valex2/kairos/KairosV1/Data/test_temp_light.csv

Timestamp | Temperature | Gas | Humidity | Pressure | Altitude | Visible Light | IR Light
0.3 | 25.8 | 147592 | 47.9 | 1009.0 | 35.1 | 145.0 | 142.0
0.6 | 25.8 | 71210 | 47.6 | 1009.0 | 35.2 | 141.0 | 143.0
0.9 | 25.9 | 86340 | 47.3 | 1009.0 | 35.2 | 141.0 | 143.0
1.2 | 25.9 | 96240 | 46.9 | 1009.0 | 35.2 | 83.0 | 77.0
1.5 | 26.0 | 102728 | 46.5 | 1009.0 | 35.2 | 113.0 | 112.0
1.8 | 26.0 | 107180 | 46.1 | 1009.0 | 35.1 | 115.0 | 111.0
2.1 | 26.1 | 112626 | 45.8 | 1009.0 | 35.1 | 111.0 | 110.0
2.4 | 26.1 | 114823 | 45.5 | 1009.0 | 35.1 | 94.0 | 91.0
2.7 | 26.1 | 116469 | 45.3 | 1009.0 | 35.1 | 119.0 | 113.0
3.0 | 26.1 | 120498 | 45.1 | 1009.0 | 35.1 | 27.0 | 30.0
3.3 | 26.1 | 123017 | 44.9 | 1009.0 | 35.1 | 24.0 | 29.0
3.59999 | 26.2 | 125091 | 44.8 | 1009.0 | 35.1 | 106.0 | 103.0
3.89999 | 26.2 | 127141 | 44.6 | 1009.0 | 35.1 | 120.0 | 115.0
4.19999 | 26.2 | 129751 | 44.4 | 1009.0 | 35.2 | 117.0 | 117.0
4.49999 | 26.2 | 130445 | 44.3 | 1009.0 | 35.1 | 120.0 | 116.0
4.79999 | 26.2 | 132470 | 44.2 | 1009.0 | 35.1 | 121.0 | 116.0
5.09999 | 26.2 | 134453 | 44.1 | 1009.0 | 35.2 | 122.0 | 121.0
5.39999 | 26.2 | 135845 | 44.0 | 1009.0 | 35.2 | 119.0 | 117.0
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
