valex2/kairos/Bootloader:UF2/Others/bootloader/feather_m4_j18/board_config.h

#ifndef BOARD_CONFIG_H
#define BOARD_CONFIG_H

#define VENDOR_NAME "Adafruit Industries"
#define PRODUCT_NAME "Feather M4 Express"
#define VOLUME_LABEL "EE156BOOT"
#define INDEX_URL "http://adafru.it/3857"
#define BOARD_ID "SAMD51J18A-FeatherM4-v0"

#define USB_VID 0x239A
#define USB_PID 0x0022

#define LED_PIN PIN_PA23

#define CRYSTALLESS    1

#define BOARD_NEOPIXEL_PIN PIN_PB03
#define BOARD_NEOPIXEL_COUNT 1

#define BOOT_USART_MODULE                 SERCOM0
#define BOOT_USART_MASK                   APBAMASK
#define BOOT_USART_BUS_CLOCK_INDEX        MCLK_APBAMASK_SERCOM0
#define BOOT_USART_PAD_SETTINGS           UART_RX_PAD3_TX_PAD0
#define BOOT_USART_PAD3                   PINMUX_PA07D_SERCOM0_PAD3
#define BOOT_USART_PAD2                   PINMUX_UNUSED
#define BOOT_USART_PAD1                   PINMUX_UNUSED
#define BOOT_USART_PAD0                   PINMUX_PA04D_SERCOM0_PAD0
#define BOOT_GCLK_ID_CORE                 SERCOM0_GCLK_ID_CORE
#define BOOT_GCLK_ID_SLOW                 SERCOM0_GCLK_ID_SLOW

#endif
