valex2/kairos/Bootloader:UF2/Others/circuitpython/samd51j18/pins.c

#include "shared-bindings/board/__init__.h"

STATIC const mp_rom_map_elem_t board_module_globals_table[] = {
    CIRCUITPYTHON_BOARD_DICT_STANDARD_ITEMS

    { MP_ROM_QSTR(MP_QSTR_PA02), MP_ROM_PTR(&pin_PA02) },
    { MP_ROM_QSTR(MP_QSTR_PA03), MP_ROM_PTR(&pin_PA03) },
    { MP_ROM_QSTR(MP_QSTR_PA04), MP_ROM_PTR(&pin_PA04) },
    { MP_ROM_QSTR(MP_QSTR_PA05), MP_ROM_PTR(&pin_PA05) },
    { MP_ROM_QSTR(MP_QSTR_PA06), MP_ROM_PTR(&pin_PA06) },
    { MP_ROM_QSTR(MP_QSTR_PA07), MP_ROM_PTR(&pin_PA07) },
    { MP_ROM_QSTR(MP_QSTR_PA08), MP_ROM_PTR(&pin_PA08) },
    { MP_ROM_QSTR(MP_QSTR_PA09), MP_ROM_PTR(&pin_PA09) },
    { MP_ROM_QSTR(MP_QSTR_PA10), MP_ROM_PTR(&pin_PA10) },
    { MP_ROM_QSTR(MP_QSTR_PA11), MP_ROM_PTR(&pin_PA11) },
    { MP_ROM_QSTR(MP_QSTR_PA12), MP_ROM_PTR(&pin_PA12) },
    { MP_ROM_QSTR(MP_QSTR_PA13), MP_ROM_PTR(&pin_PA13) },
    { MP_ROM_QSTR(MP_QSTR_PA14), MP_ROM_PTR(&pin_PA14) },
    { MP_ROM_QSTR(MP_QSTR_PA15), MP_ROM_PTR(&pin_PA15) },
    { MP_ROM_QSTR(MP_QSTR_PA16), MP_ROM_PTR(&pin_PA16) },
    { MP_ROM_QSTR(MP_QSTR_PA17), MP_ROM_PTR(&pin_PA17) },
    { MP_ROM_QSTR(MP_QSTR_PA18), MP_ROM_PTR(&pin_PA18) },
    { MP_ROM_QSTR(MP_QSTR_PA19), MP_ROM_PTR(&pin_PA19) },
    { MP_ROM_QSTR(MP_QSTR_PA20), MP_ROM_PTR(&pin_PA20) },
    { MP_ROM_QSTR(MP_QSTR_PA21), MP_ROM_PTR(&pin_PA21) },
    { MP_ROM_QSTR(MP_QSTR_PA22), MP_ROM_PTR(&pin_PA22) },
    { MP_ROM_QSTR(MP_QSTR_PA23), MP_ROM_PTR(&pin_PA23) },
    { MP_ROM_QSTR(MP_QSTR_PA27), MP_ROM_PTR(&pin_PA27) },
    { MP_ROM_QSTR(MP_QSTR_PA30), MP_ROM_PTR(&pin_PA30) },
    { MP_ROM_QSTR(MP_QSTR_PA31), MP_ROM_PTR(&pin_PA31) },

    { MP_ROM_QSTR(MP_QSTR_PB00), MP_ROM_PTR(&pin_PB00) },
    { MP_ROM_QSTR(MP_QSTR_PB01), MP_ROM_PTR(&pin_PB01) },
    { MP_ROM_QSTR(MP_QSTR_PB02), MP_ROM_PTR(&pin_PB02) },
    { MP_ROM_QSTR(MP_QSTR_PB03), MP_ROM_PTR(&pin_PB03) },
    { MP_ROM_QSTR(MP_QSTR_PB04), MP_ROM_PTR(&pin_PB04) },
    { MP_ROM_QSTR(MP_QSTR_PB05), MP_ROM_PTR(&pin_PB05) },
    { MP_ROM_QSTR(MP_QSTR_PB06), MP_ROM_PTR(&pin_PB06) },
    { MP_ROM_QSTR(MP_QSTR_PB07), MP_ROM_PTR(&pin_PB07) },
    { MP_ROM_QSTR(MP_QSTR_PB08), MP_ROM_PTR(&pin_PB08) },
    { MP_ROM_QSTR(MP_QSTR_PB09), MP_ROM_PTR(&pin_PB09) },
    { MP_ROM_QSTR(MP_QSTR_PB10), MP_ROM_PTR(&pin_PB10) },
    { MP_ROM_QSTR(MP_QSTR_PB11), MP_ROM_PTR(&pin_PB11) },
    { MP_ROM_QSTR(MP_QSTR_PB12), MP_ROM_PTR(&pin_PB12) },
    { MP_ROM_QSTR(MP_QSTR_PB13), MP_ROM_PTR(&pin_PB13) },
    { MP_ROM_QSTR(MP_QSTR_PB14), MP_ROM_PTR(&pin_PB14) },
    { MP_ROM_QSTR(MP_QSTR_PB15), MP_ROM_PTR(&pin_PB15) },
    { MP_ROM_QSTR(MP_QSTR_PB16), MP_ROM_PTR(&pin_PB16) },
    { MP_ROM_QSTR(MP_QSTR_PB17), MP_ROM_PTR(&pin_PB17) },
    { MP_ROM_QSTR(MP_QSTR_PB22), MP_ROM_PTR(&pin_PB22) },
    { MP_ROM_QSTR(MP_QSTR_PB23), MP_ROM_PTR(&pin_PB23) },
    { MP_ROM_QSTR(MP_QSTR_PB30), MP_ROM_PTR(&pin_PB30) },
    { MP_ROM_QSTR(MP_QSTR_PB31), MP_ROM_PTR(&pin_PB31) },
    

    { MP_ROM_QSTR(MP_QSTR_I2C), MP_ROM_PTR(&board_i2c_obj) },
    { MP_ROM_QSTR(MP_QSTR_SPI), MP_ROM_PTR(&board_spi_obj) },
    { MP_ROM_QSTR(MP_QSTR_UART), MP_ROM_PTR(&board_uart_obj) },
};
MP_DEFINE_CONST_DICT(board_module_globals, board_module_globals_table);
